nickthelegend/xorr-pad/docs/images/caps-outline.png

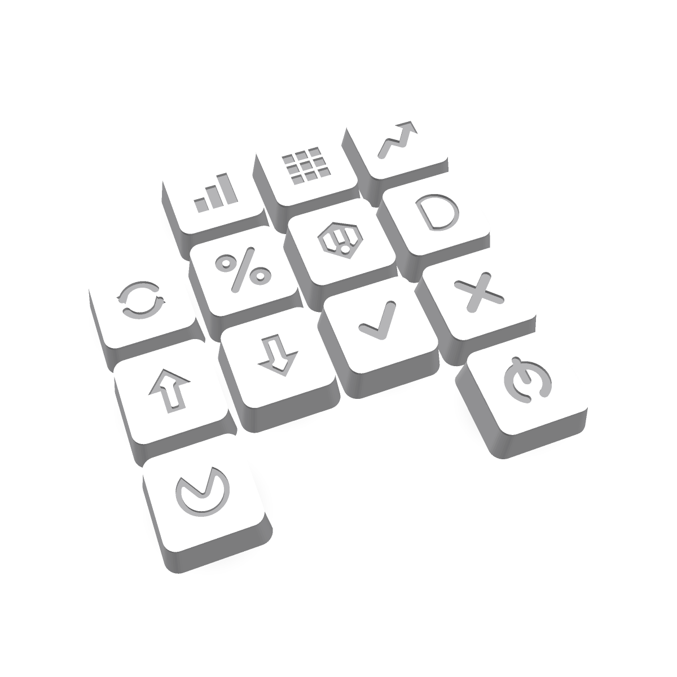
docs/images/caps-outline.png
