nickthelegend/xorr-pad/docs/images/display-pod-24-cover.png

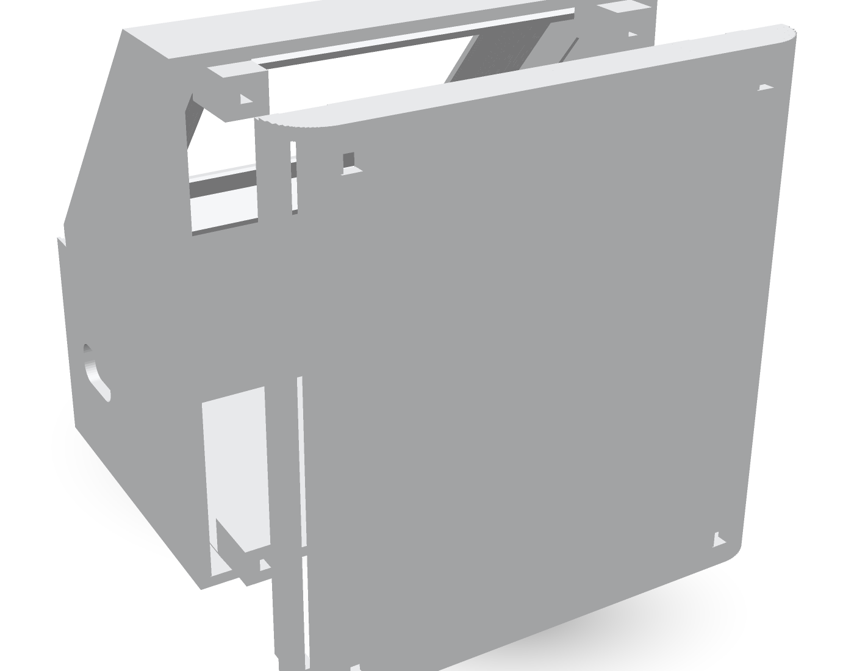
docs/images/display-pod-24-cover.png
