nickthelegend/xorr-pad/docs/images/display-pod-24.png

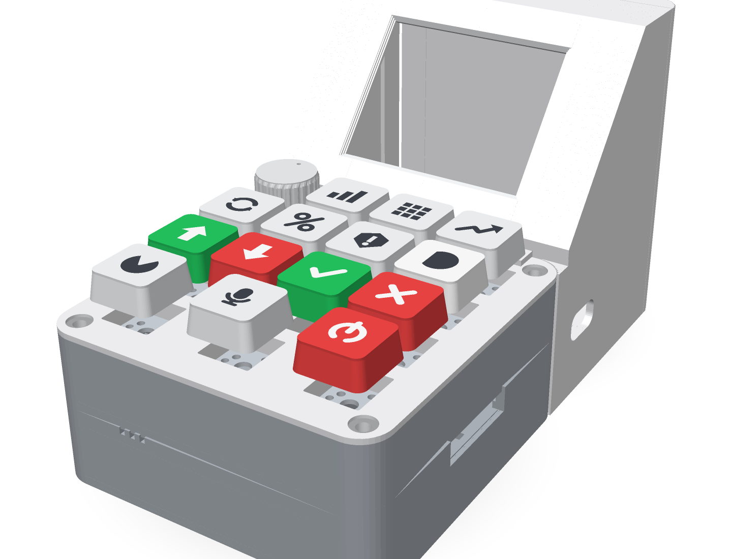
docs/images/display-pod-24.png
