nickthelegend/xorr-pad/docs/images/display-pod-28-side.png

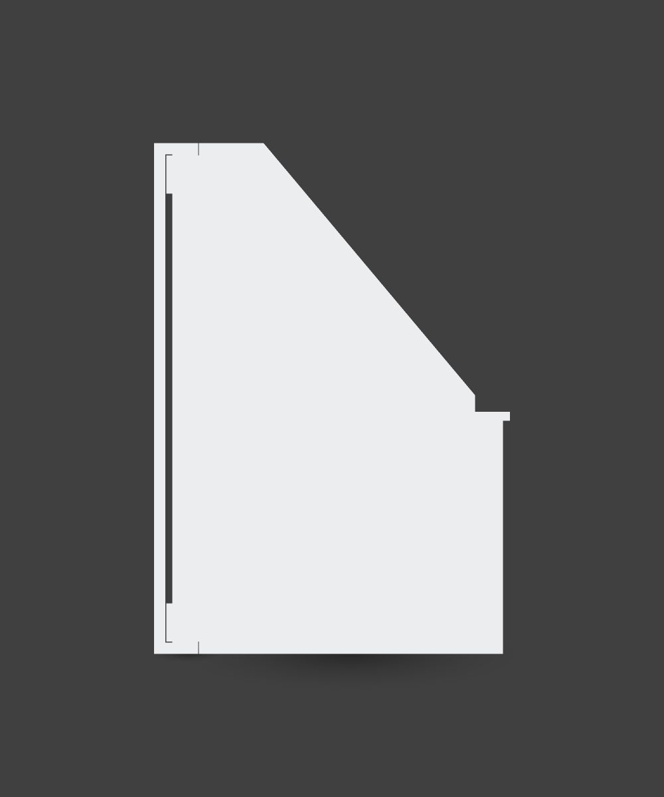
docs/images/display-pod-28-side.png
