nickthelegend/xorr-pad/docs/images/display-pod-28.png

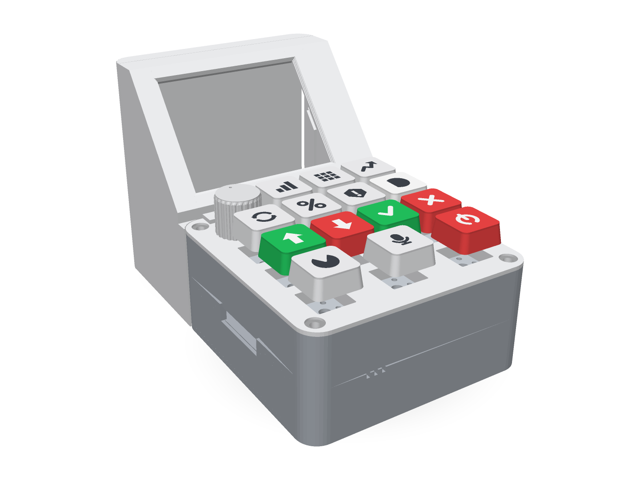
docs/images/display-pod-28.png
