nickthelegend/xorr-pad/docs/images/display-pod-back.png

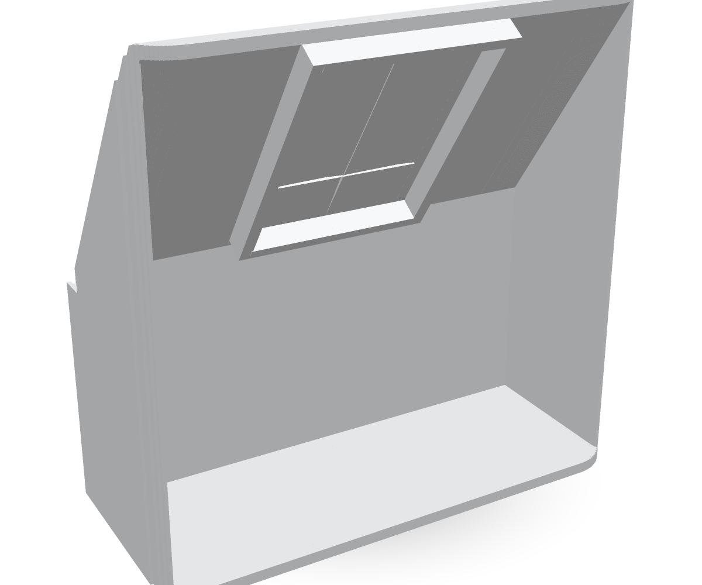
docs/images/display-pod-back.png
