nickthelegend/xorr-pad/docs/images/display-pod-side.png

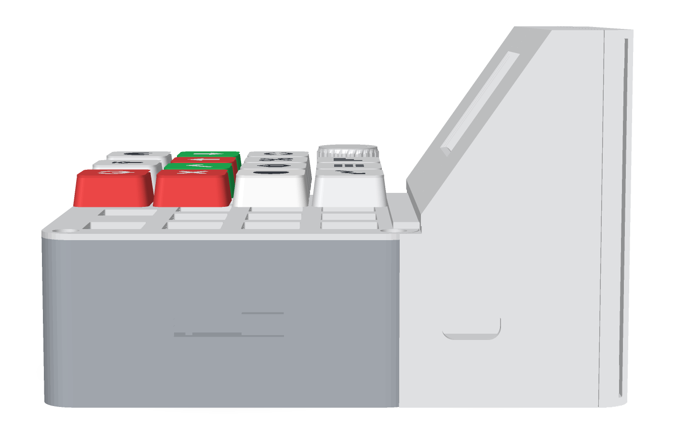
docs/images/display-pod-side.png
