nickthelegend/xorr-pad/docs/images/display-pod.png

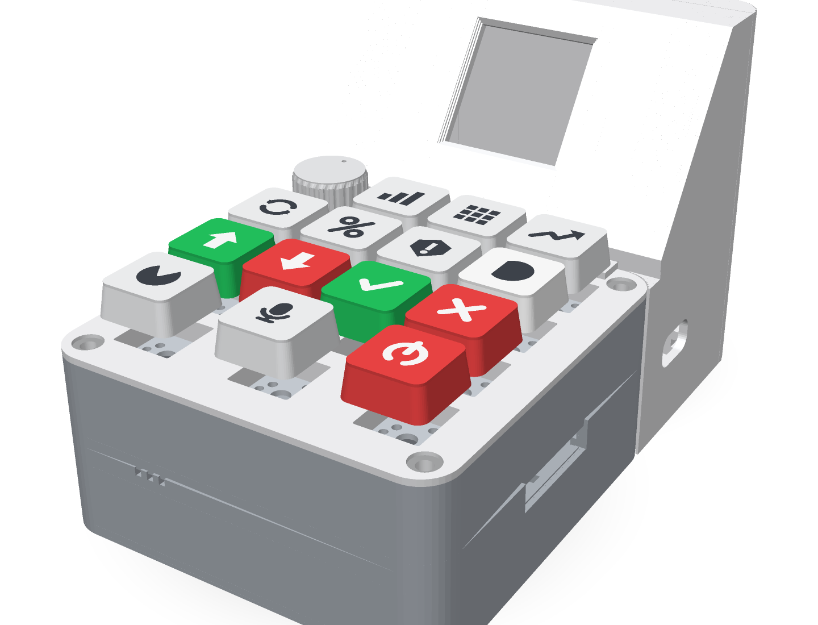
docs/images/display-pod.png
