nickthelegend/xorr-pad/docs/images/exploded.png

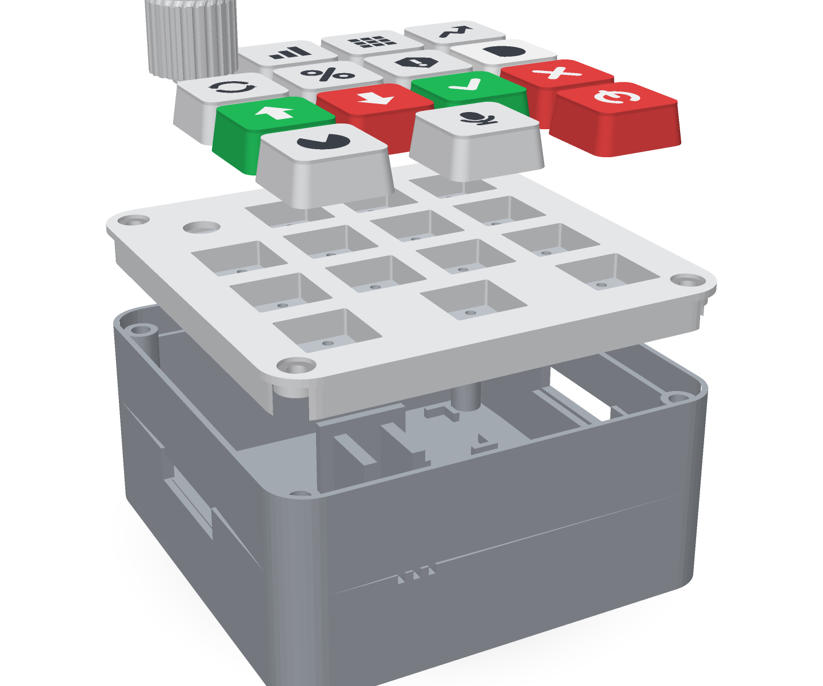
docs/images/exploded.png
