nickthelegend/xorr-pad/docs/images/hero.png

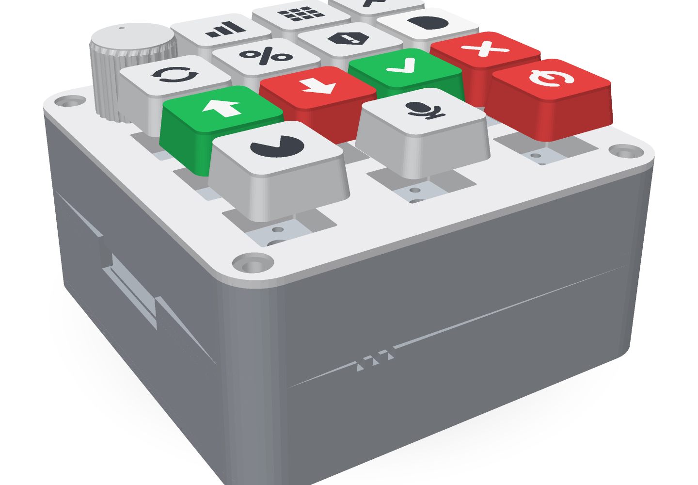
docs/images/hero.png
