nickthelegend/xorr-pad/docs/images/knob-clip.png

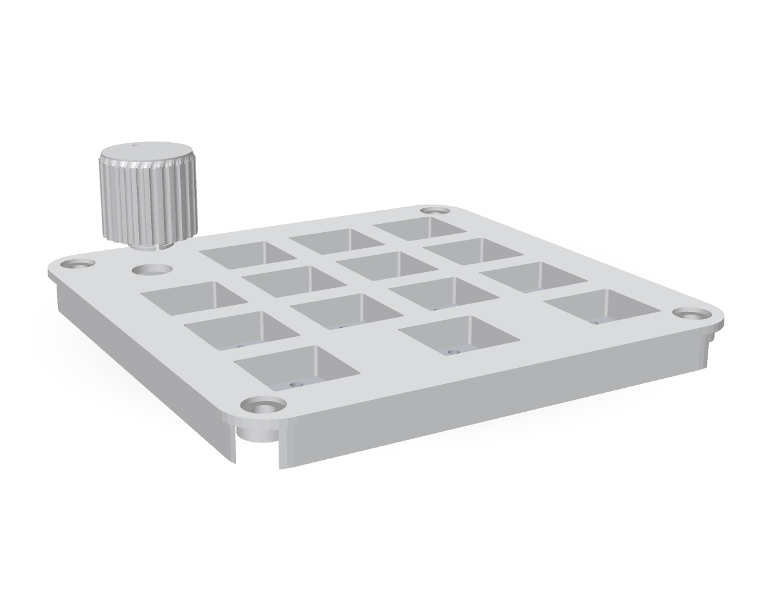
docs/images/knob-clip.png
