nickthelegend/xorr-pad/docs/images/plate-underside.png

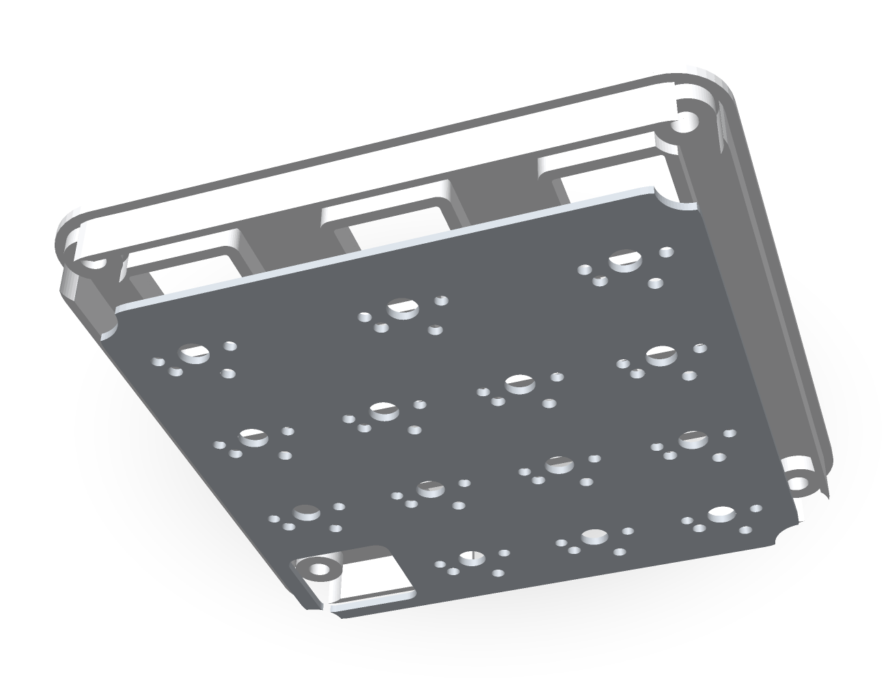
docs/images/plate-underside.png
