nickthelegend/xorr-pad/docs/images/tray-bay.png

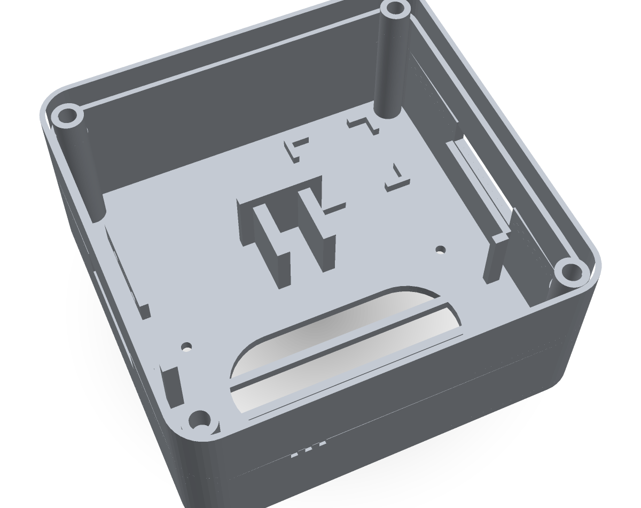
docs/images/tray-bay.png
