nickthelegend/xorr-pad/docs/images/tray-right.png

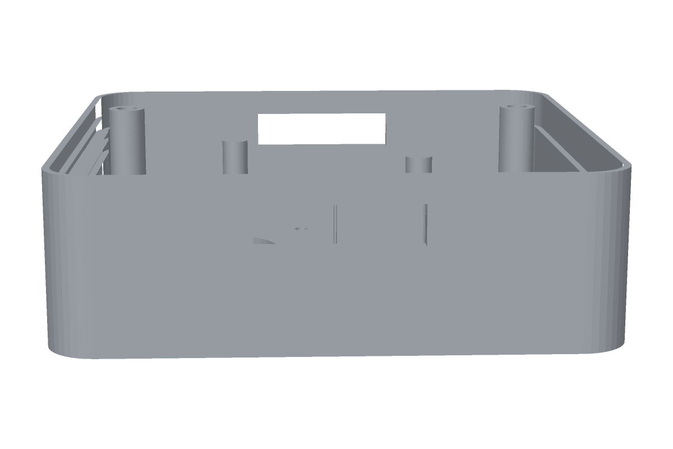
docs/images/tray-right.png
