nickthelegend/xorr-pad/docs/images/parts.png

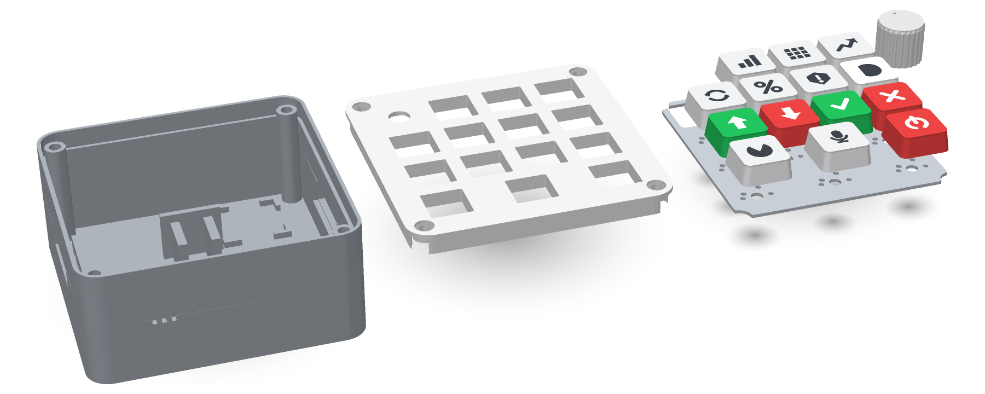
docs/images/parts.png
