nickthelegend/xorr-pad/exports/display-coupon.stl

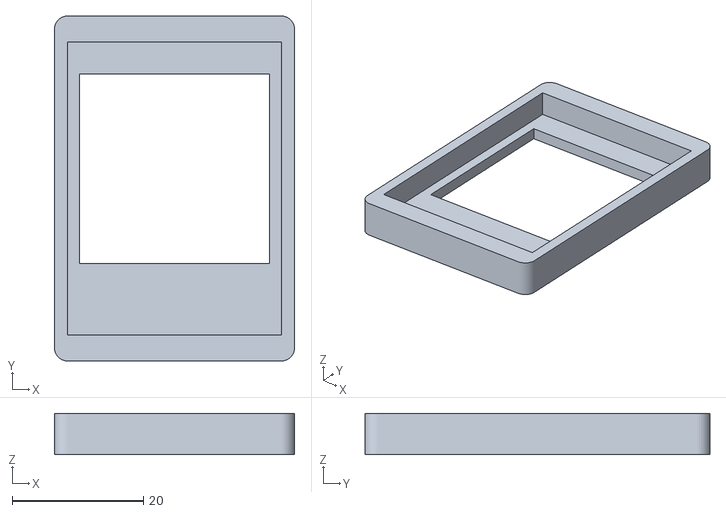
[picture p38: CAD file, 2026-09-12]
exports/display-coupon.stl
36.6 x 52.6 x 6.30
