nickthelegend/xorr-pad/exports/print/caps-green.stl

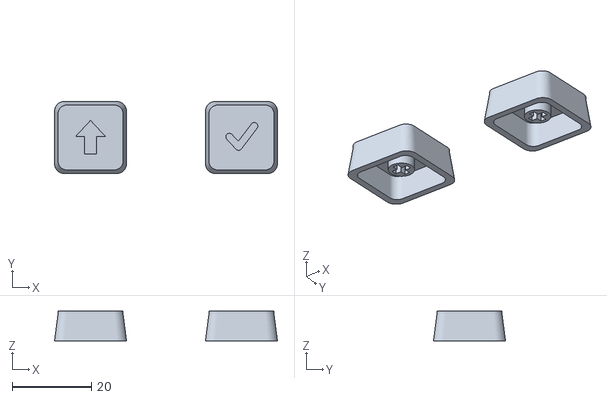
[picture p39: CAD file, 2026-09-07]
exports/print/caps-green.stl
56.3 x 18.2 x 7.50
