nickthelegend/xorr-pad/exports/display-coupon-24.stl

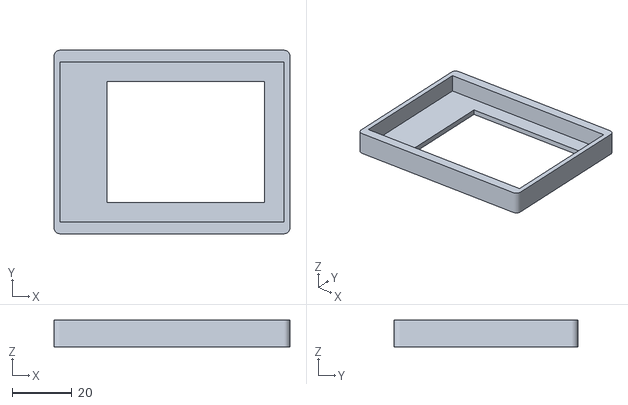
[picture p40: CAD file, 2026-09-12]
exports/display-coupon-24.stl
78.8 x 61.3 x 8.90
