nickthelegend/xorr-pad/exports/print/legends-white.stl

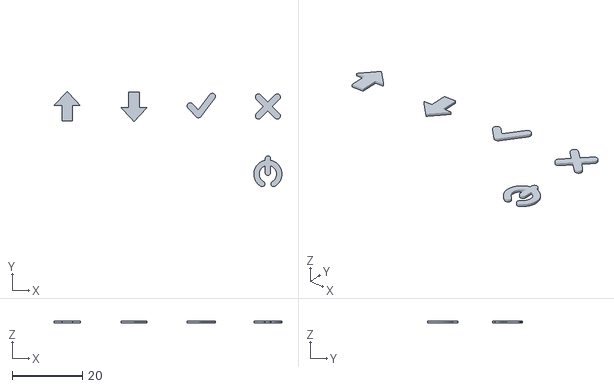
[picture p41: CAD file, 2026-09-07]
exports/print/legends-white.stl
64.9 x 27.1 x 0.6
