nickthelegend/xorr-pad/exports/plate.stl

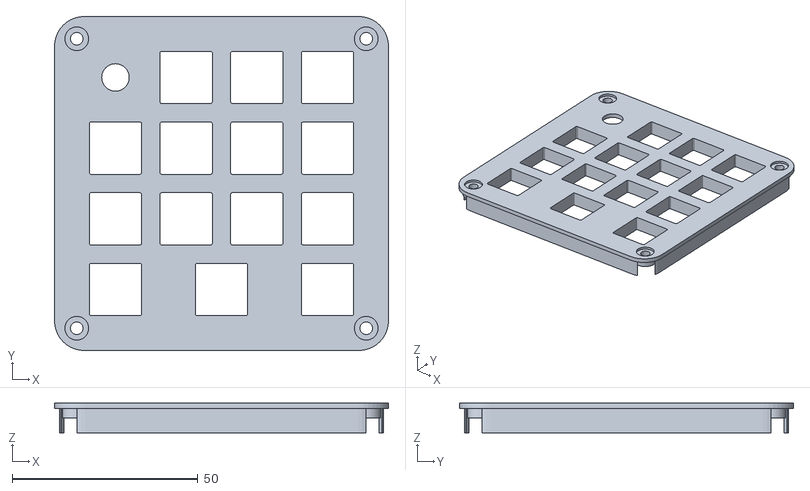
[picture p42: CAD file, 2026-09-07]
exports/plate.stl
90.0 x 90.0 x 8.00
