nickthelegend/xorr-pad/exports/print/caps-red.stl

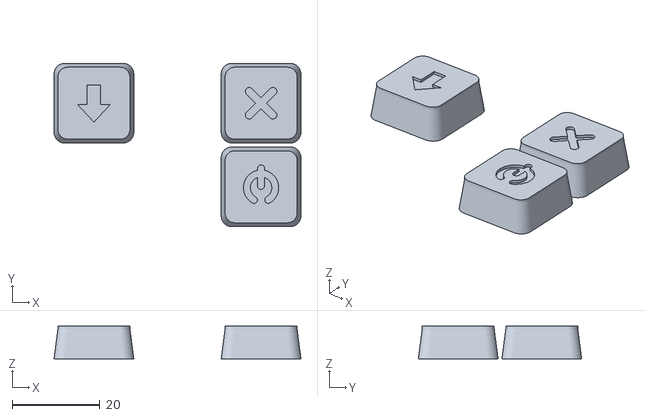
[picture p43: CAD file, 2026-09-07]
exports/print/caps-red.stl
56.3 x 37.2 x 7.50
