nickthelegend/xorr-pad/exports/knob.stl

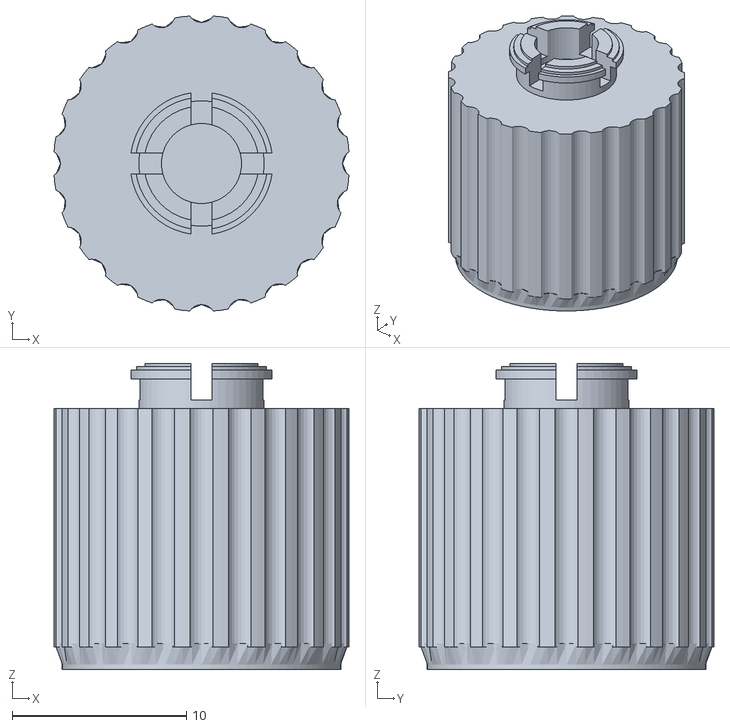
[picture p44: CAD file, 2026-09-07]
exports/knob.stl
16.9 x 16.9 x 17.6
