nickthelegend/xorr-pad/exports/tray.stl

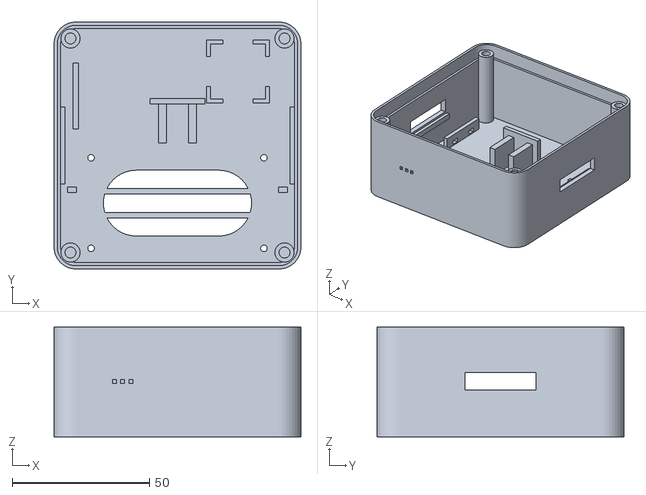
[picture p45: CAD file, 2026-09-07]
exports/tray.stl
90.0 x 90.0 x 40.0
