nickthelegend/xorr-pad/exports/caps-all.stl

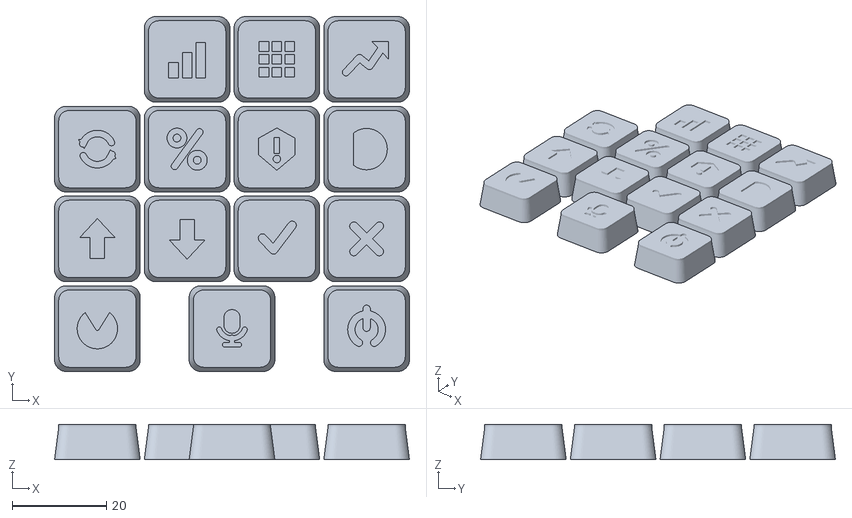
[picture p46: CAD file, 2026-09-07]
exports/caps-all.stl
75.3 x 75.3 x 7.50
