nickthelegend/xorr-pad/exports/legends-all.stl

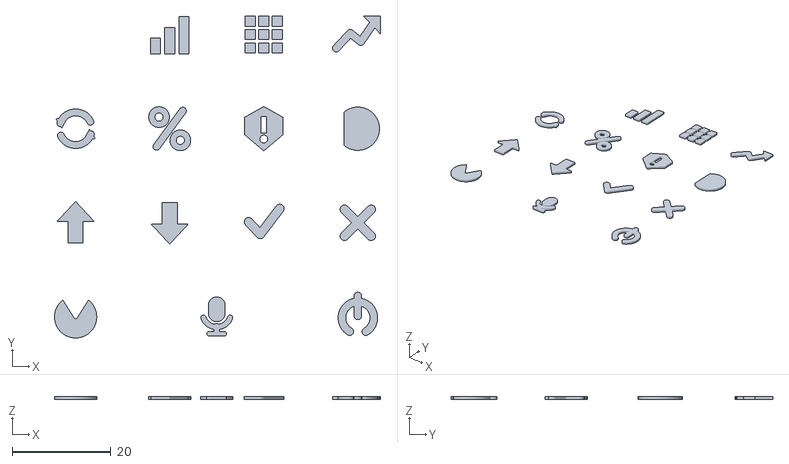
[picture p47: CAD file, 2026-09-07]
exports/legends-all.stl
66.0 x 65.2 x 0.6
