nickthelegend/xorr-pad/exports/switch-deck.stl

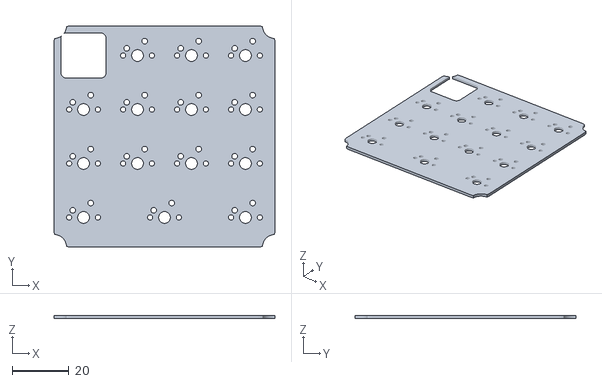
[picture p48: CAD file, 2026-09-07]
exports/switch-deck.stl
78.0 x 78.0 x 1.20
